Alberto0235/DRSSTC-Fiber-Optic-Interrupter/Hardware/KiCad/Interrupter/Fiber_Outputs.kicad_sch

## KiCad design Hardware/KiCad/Interrupter/Fiber_Outputs.kicad_sch (2026-04-12)

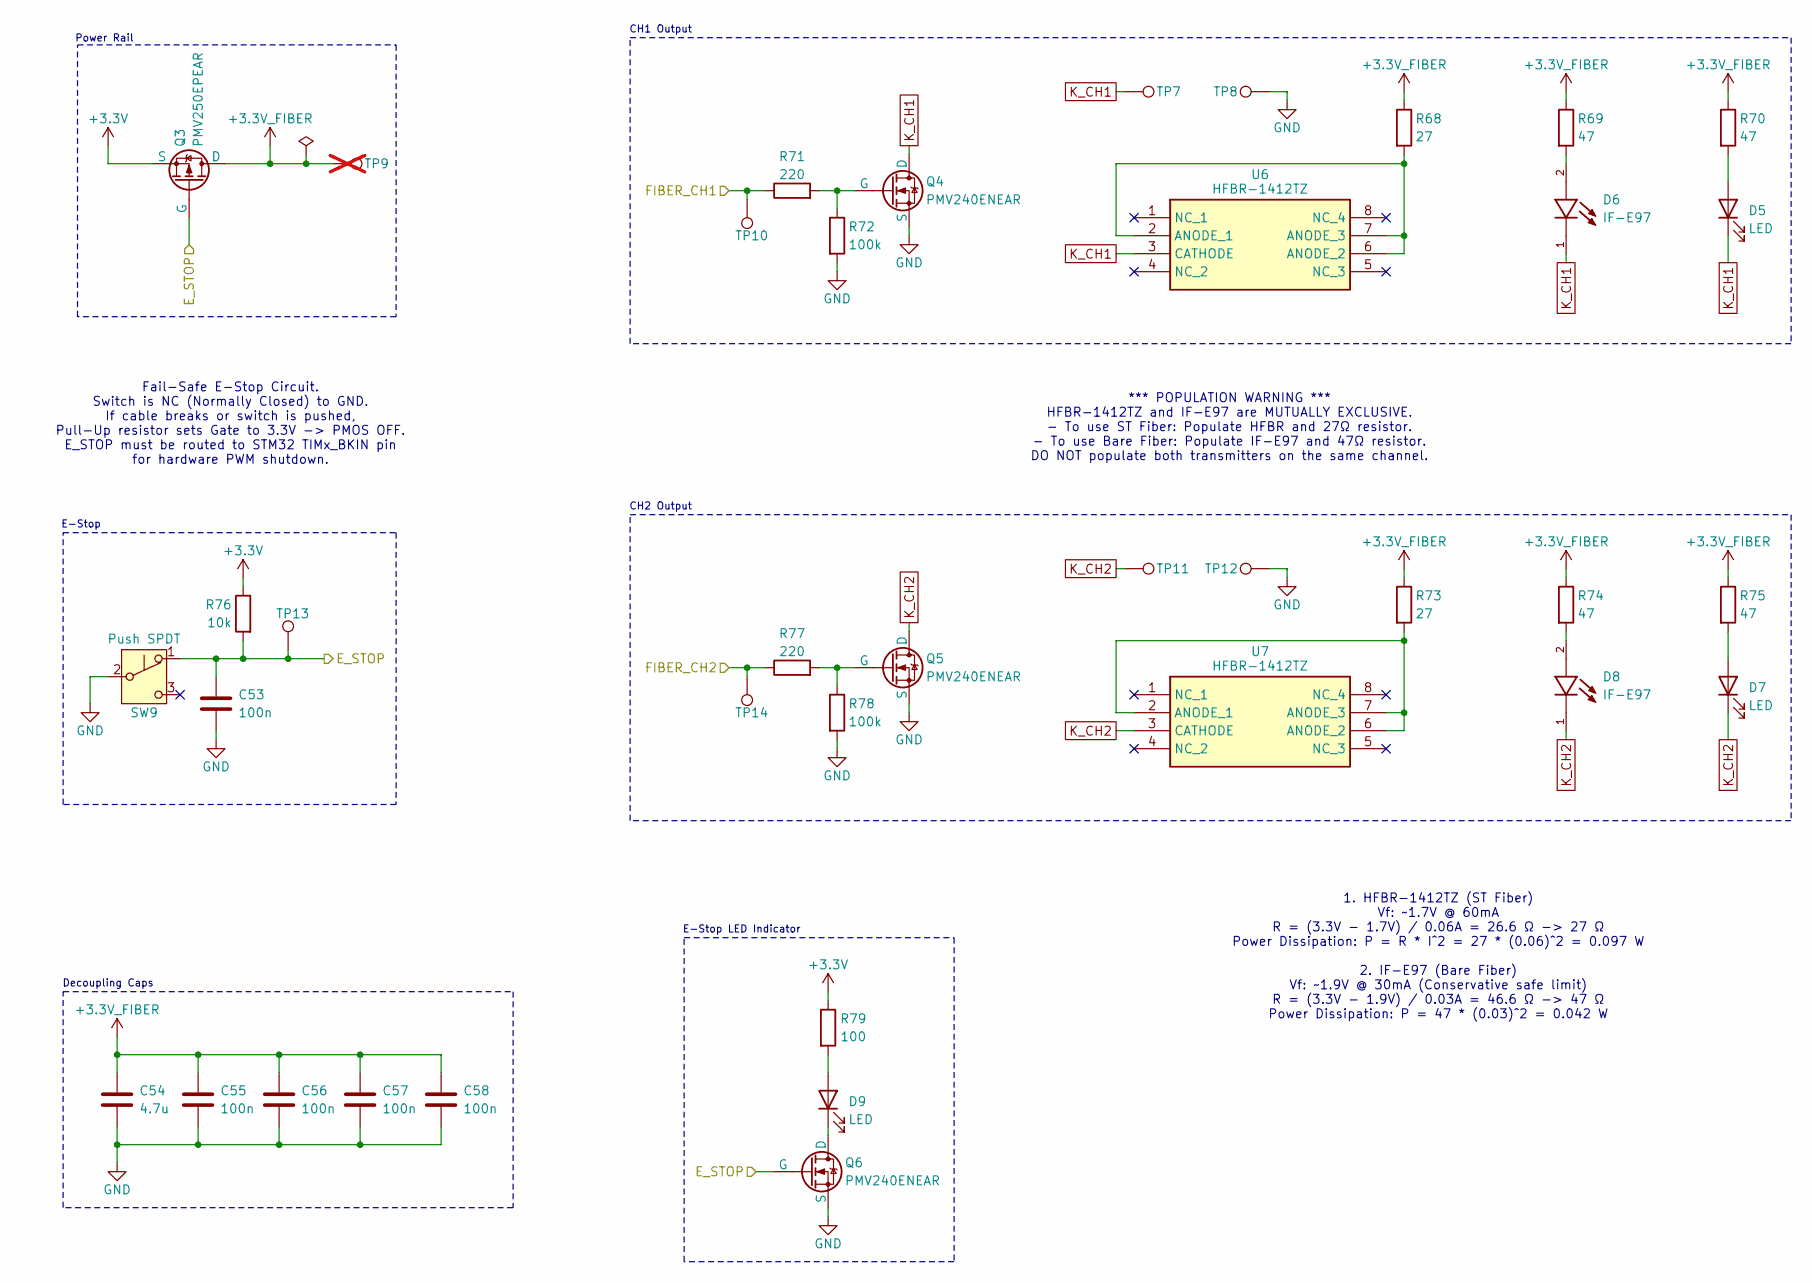
[picture p9: schematic Fiber_Outputs.kicad_sch]

Parts:
C53, C55, C56, C57, C58: 100n; C_0402_1005Metric; Manufacturer_Part_Number GRT155R71H104KE01J
C54: 4.7u; C_0805_2012Metric; Manufacturer_Part_Number GRM21BZ7YA475KE15K
D5, D7: LED; TOPLED E1608; Manufacturer_Part_Number KB DELSS2.12-THUH-34-2686
D6, D8: IF-E97; PARTREV 11/20
D9: LED; TOPLED E1608; Manufacturer_Part_Number KS DELPS1.22-TIVH-68-H3Q4-20-S
Q3: PMV250EPEAR; SOT-23; Manufacturer_Part_Number PMV250EPEA
Q4, Q5, Q6: PMV240ENEAR; SOT-23; Manufacturer_Part_Number PMV240ENEAR
R68, R73: 27; R_0805_2012Metric; Manufacturer_Part_Number ERJ-P06F27R0V
R69, R70, R74, R75: 47; R_0805_2012Metric; Manufacturer_Part_Number ERJ-P06F47R0V
R71, R77: 220; R_0402_1005Metric; Manufacturer_Part_Number AC0402FR-7W220RL
R72, R78: 100k; R_0402_1005Metric; Manufacturer_Part_Number AC0402FR-7W100KL
R76: 10k; R_0402_1005Metric; Manufacturer_Part_Number AC0402FR-0710KL
R79: 100; R_0402_1005Metric; Manufacturer_Part_Number AC0402FR-13100RL
SW9: Push SPDT; 8161SHCQE2; Manufacturer_Part_Number 8161SHCQE2
TP7, TP8, TP10, TP11, TP12, TP13, TP14: TestPoint; S275146R; Manufacturer_Part_Number S2751-46R
TP9: TestPoint; S275146R; Manufacturer_Part_Number S2751-46R; not fitted
U6, U7: HFBR-1412TZ; HFBR1412TMZ; Mouser Part Number 630-HFBR-1412TZ

Connections:
+3.3V: Q3.2 (S), R76.1, R79.1
+3.3V_FIBER: C54.1, C55.1, C56.1, C57.1, C58.1, Q3.3 (D), R68.1, R69.1, R70.1, R73.1, R74.1, R75.1, TP9.1
E_STOP: C53.1, Q3.1 (G), Q6.1 (G), R76.2, SW9.1 (A), TP13.1
FIBER_CH1: R71.1, TP10.1
FIBER_CH2: R77.1, TP14.1
GND: C53.2, C54.2, C55.2, C56.2, C57.2, C58.2, Q4.2 (S), Q5.2 (S), Q6.2 (S), R72.2, R78.2, SW9.2 (B), TP8.1, TP12.1
K_CH1: D5.1 (K), D6.1, Q4.3 (D), TP7.1, U6.3 (CATHODE)
K_CH2: D7.1 (K), D8.1, Q5.3 (D), TP11.1, U7.3 (CATHODE)
unnamed: D5.2 (A), R70.2
unnamed: D6.2, R69.2
unnamed: D7.2 (A), R75.2
unnamed: D8.2, R74.2
unnamed: D9.1 (K), Q6.3 (D)
unnamed: D9.2 (A), R79.2
unnamed: Q4.1 (G), R71.2, R72.1
unnamed: Q5.1 (G), R77.2, R78.1
unnamed: R68.2, U6.2 (ANODE_1), U6.6 (ANODE_2), U6.7 (ANODE_3)
unnamed: R73.2, U7.2 (ANODE_1), U7.6 (ANODE_2), U7.7 (ANODE_3)

Notes on the sheet:
Power Rail
CH1 Output
*** POPULATION WARNING *** HFBR-1412TZ and IF-E97 are MUTUALLY EXCLUSIVE. - To use ST Fiber: Populate HFBR and 27Ω resistor. - To use Bare Fiber: Populate IF-E97 and 47Ω resistor. DO NOT populate both transmitters on the same channel.
E-Stop LED Indicator
1. HFBR-1412TZ (ST Fiber) Vf: ~1.7V @ 60mA R = (3.3V - 1.7V) / 0.06A = 26.6 Ω -> 27 Ω Power Dissipation: P = R * I^2 = 27 * (0.06)^2 = 0.097 W 2. IF-E97 (Bare Fiber) Vf: ~1.9V @ 30mA (Conservative safe limit) R = (3.3V - 1.9V) / 0.03A = 46.6 Ω -> 47 Ω Power Dissipation: P = 47 * (0.03)^2 = 0.042 W
Fail-Safe E-Stop Circuit. Switch is NC (Normally Closed) to GND. If cable breaks or switch is pushed, Pull-Up resistor sets Gate to 3.3V -> PMOS OFF. E_STOP must be routed to STM32 TIMx_BKIN pin for hardware PWM shutdown.
CH2 Output
E-Stop
Decoupling Caps
