Alberto0235/DRSSTC-Fiber-Optic-Interrupter/Hardware/KiCad/Interrupter/Interrupter v1.2.kicad_sch

## KiCad design Hardware/KiCad/Interrupter/Interrupter v1.2.kicad_sch (2026-04-03)

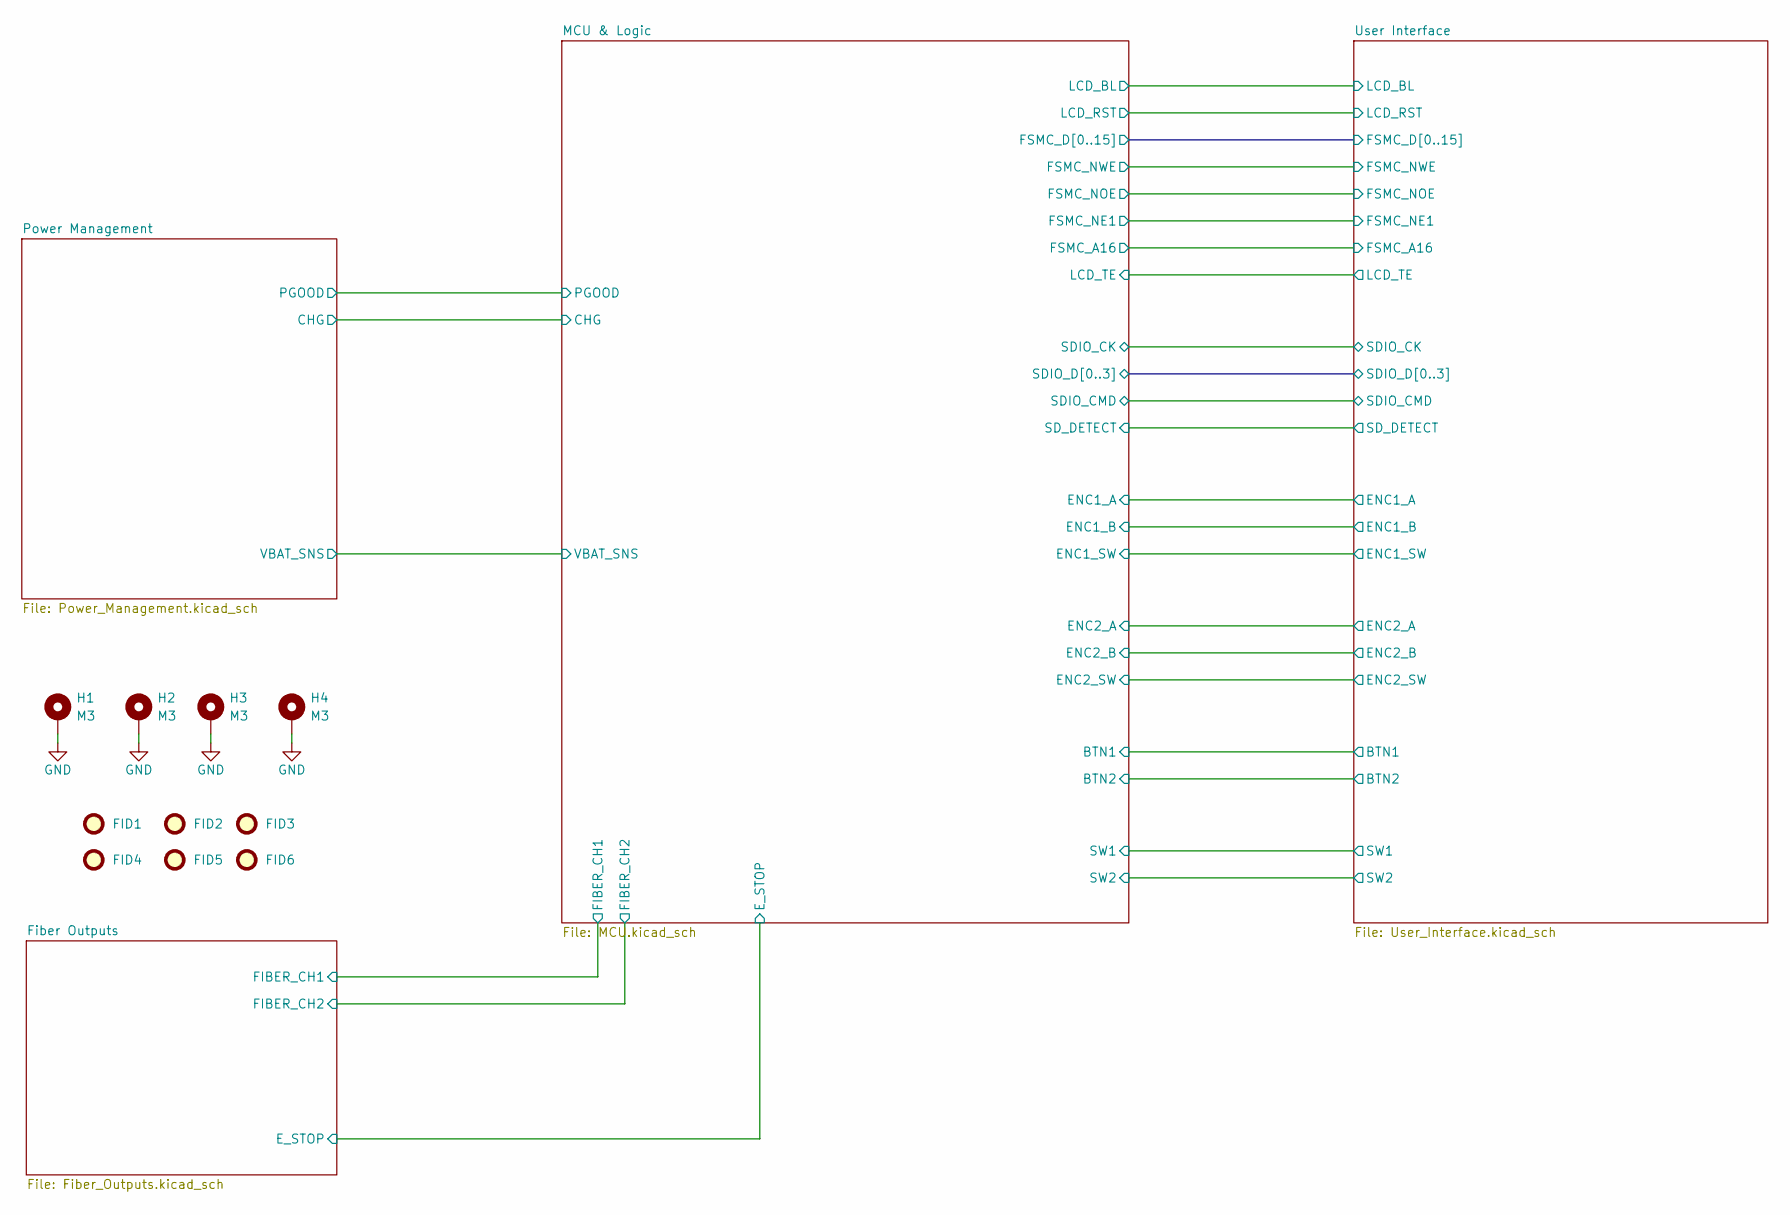
[picture p10: schematic Interrupter v1.2.kicad_sch]

Parts:
FID1, FID2, FID3, FID4, FID5, FID6: Fiducial; Fiducial_1mm_Mask2mm; Manufacturer_Part_Number Fiducial
H1, H2, H3, H4: M3; MountingHole_3.2mm_M3_Pad_Via; Manufacturer_Part_Number MountingHole-M3

Connections:
GND: H1.1, H2.1, H3.1, H4.1
