Alberto0235/DRSSTC-Fiber-Optic-Interrupter/Hardware/KiCad/Interrupter/mcu.kicad_sch

## KiCad design Hardware/KiCad/Interrupter/mcu.kicad_sch (2026-04-12)

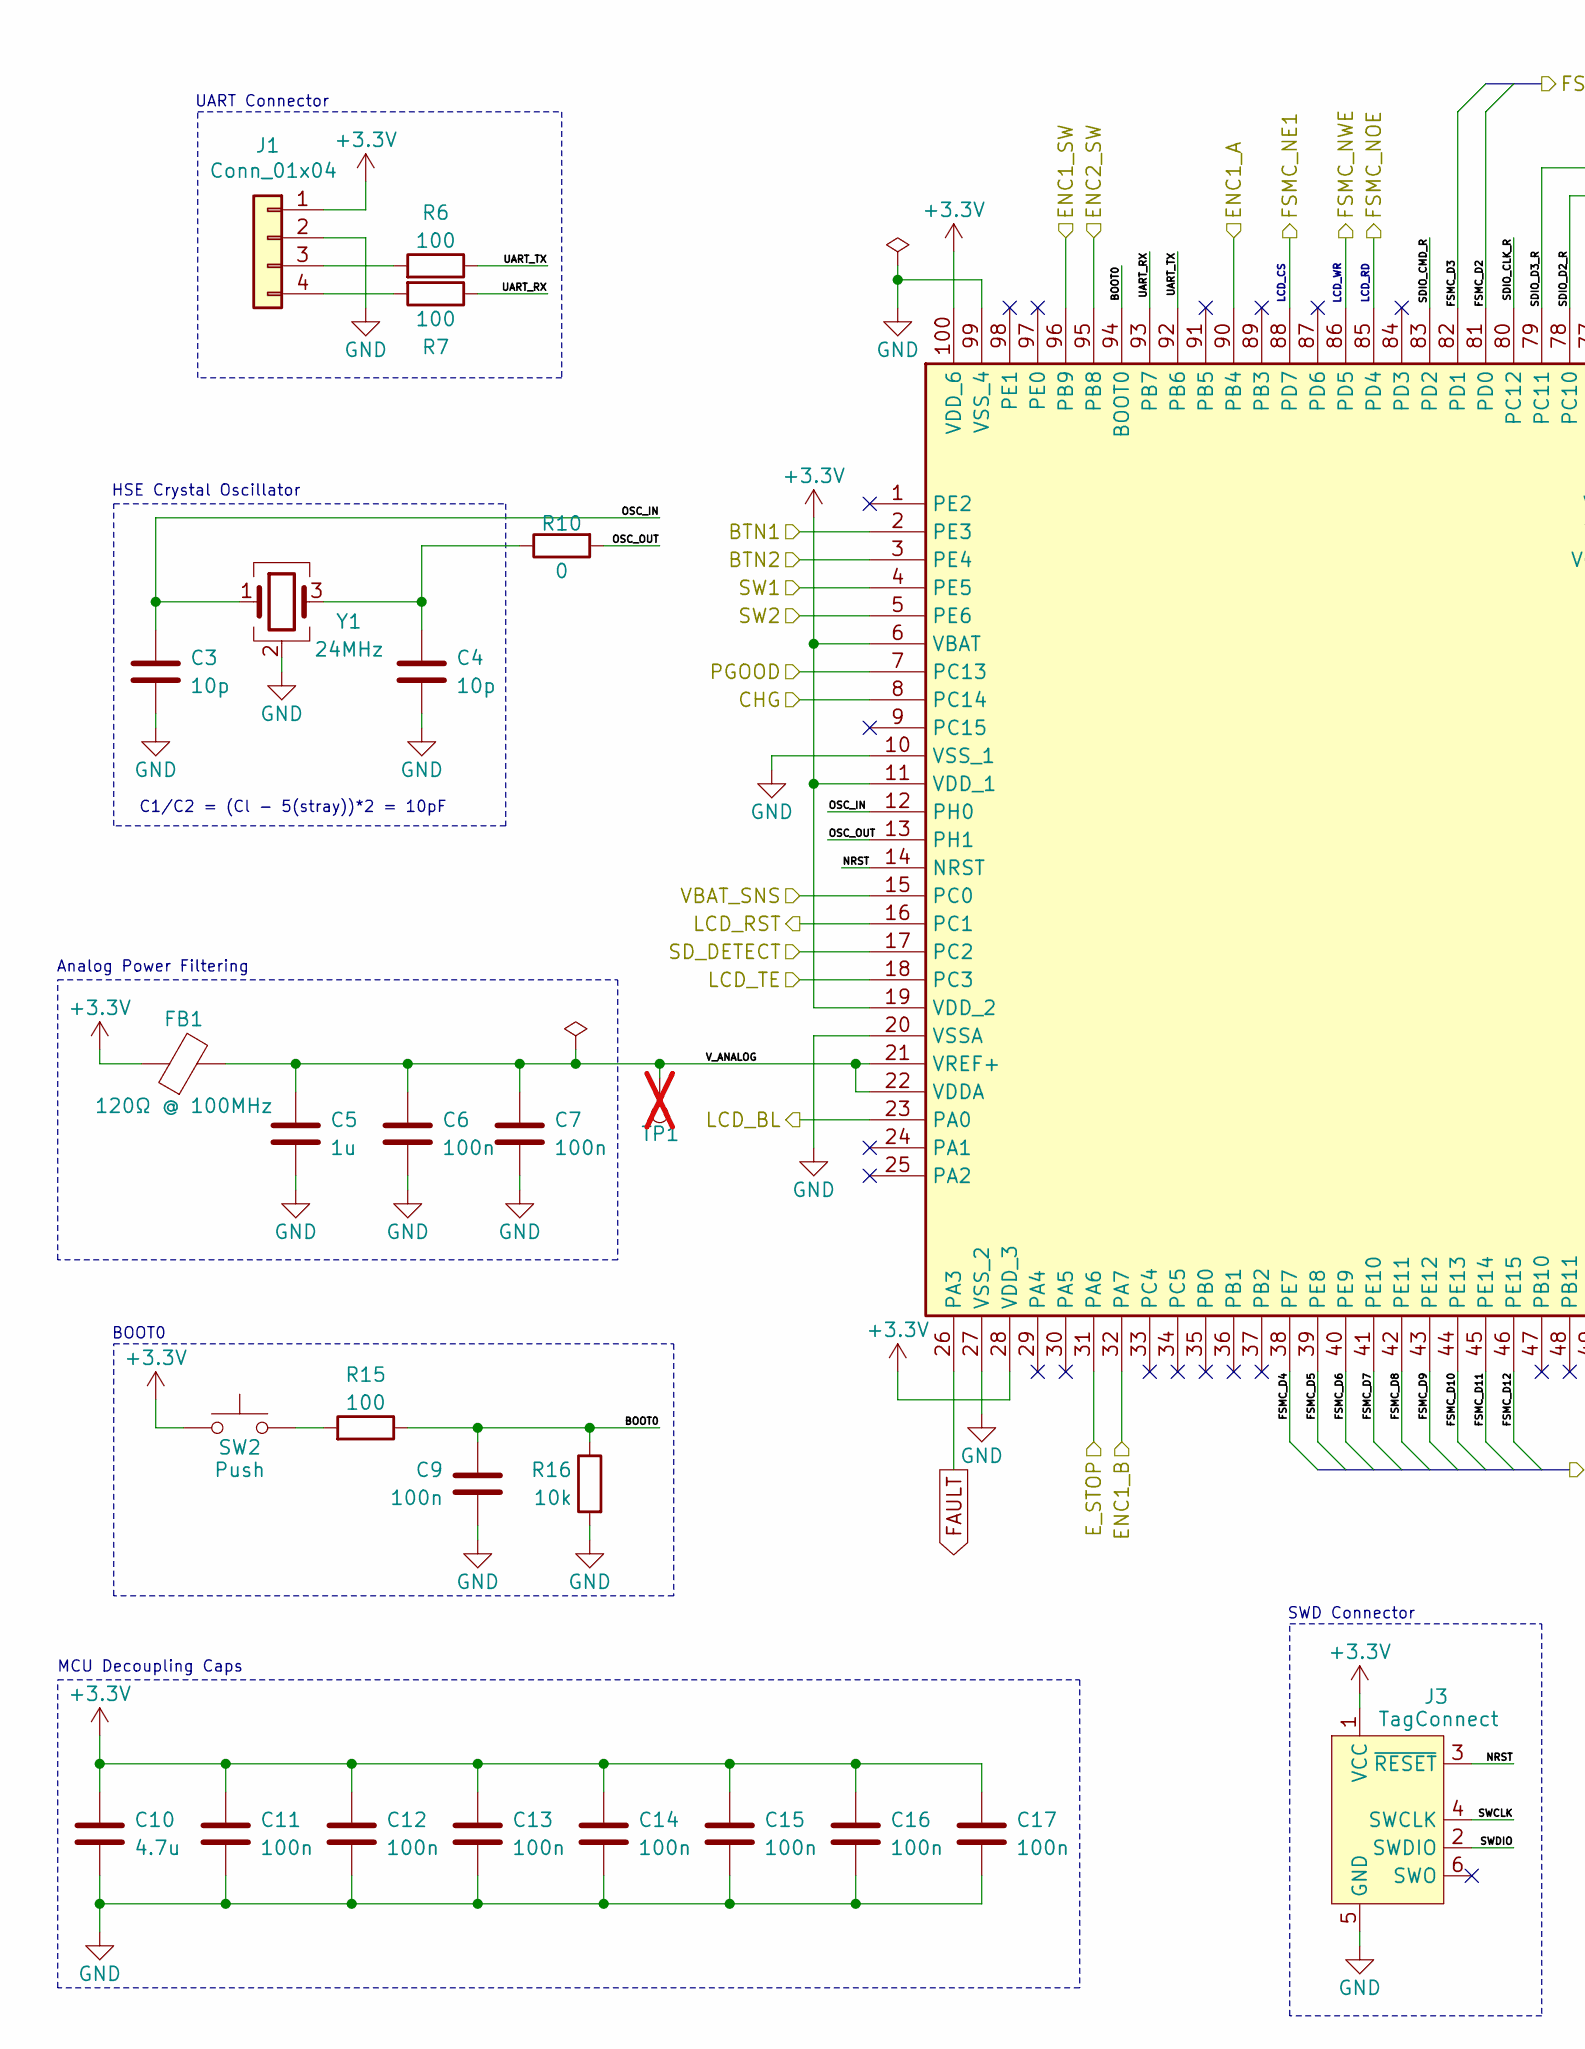
[picture p11: schematic mcu.kicad_sch, part in row 1, column 1]

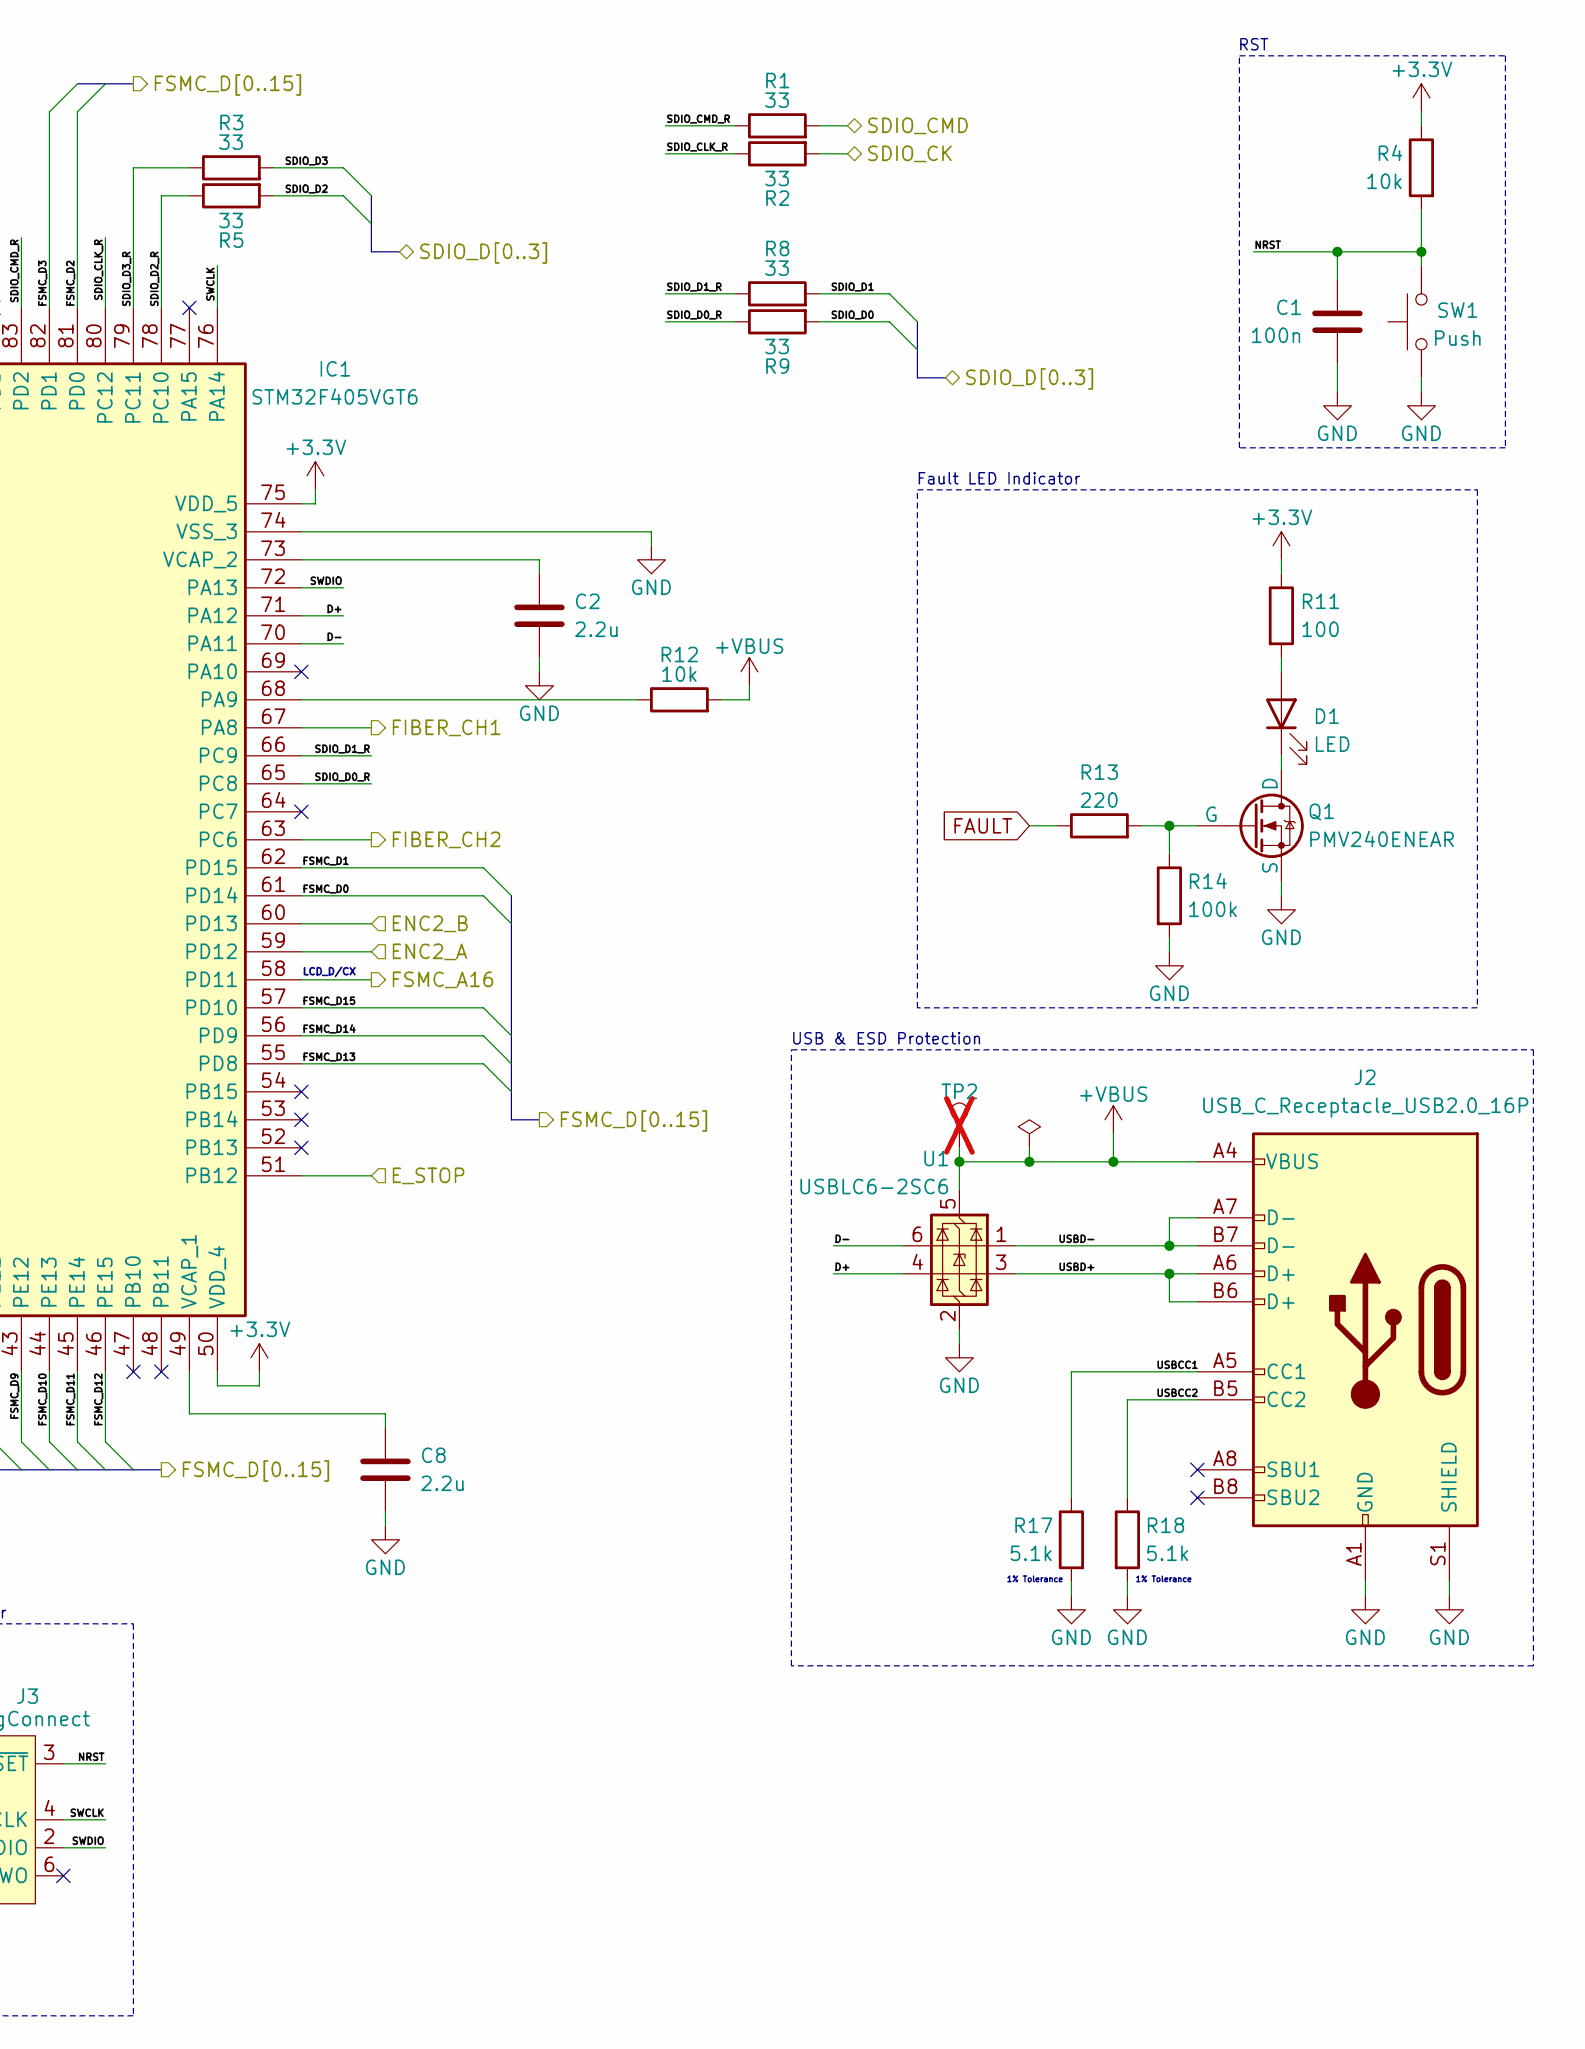
[picture p12: schematic mcu.kicad_sch, part in row 1, column 2]

Parts:
C1, C6, C7, C9, C11, C12, C13, C14, C15, C16, C17: 100n; C_0402_1005Metric; Manufacturer_Part_Number GRT155R71H104KE01J
C2, C8: 2.2u; C_0805_2012Metric; Manufacturer_Part_Number KGM21AR71E225KU
C3, C4: 10p; C_0402_1005Metric; Manufacturer_Part_Number GRM1555C1H100FA01D
C5: 1u; C_0603_1608Metric; Manufacturer_Part_Number C1608X7R1H105K080AB
C10: 4.7u; C_0805_2012Metric; Manufacturer_Part_Number GRM21BZ7YA475KE15K
D1: LED; TOPLED E1608; Manufacturer_Part_Number KS DELPS1.22-TIVH-68-H3Q4-20-S
FB1: 120Ω @ 100MHz; L_0603_1608Metric; Manufacturer_Part_Number BLM18SG121TZ1D
IC1: STM32F405VGT6; Mouser Part Number 511-STM32F405VGT6
J1: Conn_01x04; PinSocket_1x04_P2.00mm_Vertical
J2: USB_C_Receptacle_USB2.0_16P; USB_C_Receptacle_GCT_USB4105-xx-A_16P_TopMnt_Horizontal; Manufacturer_Part_Number USB4105-GF-A-120
J3: TagConnect; Tag-Connect_TC2030-IDC-NL_2x03_P1.27mm_Vertical
Q1: PMV240ENEAR; SOT-23; Manufacturer_Part_Number PMV240ENEAR
R1, R2, R3, R5, R8, R9: 33; R_0402_1005Metric; Manufacturer_Part_Number RCA040233R0FKEDSR
R4, R12, R16: 10k; R_0402_1005Metric; Manufacturer_Part_Number AC0402FR-0710KL
R6, R7, R11, R15: 100; R_0402_1005Metric; Manufacturer_Part_Number AC0402FR-13100RL
R10: 0; R_0402_1005Metric; Manufacturer_Part_Number CRCW04020000Z0ED
R13: 220; R_0402_1005Metric; Manufacturer_Part_Number AC0402FR-7W220RL
R14: 100k; R_0402_1005Metric; Manufacturer_Part_Number AC0402FR-7W100KL
R17, R18: 5.1k; R_0402_1005Metric; Manufacturer_Part_Number AF0402FR-075K1L
SW1, SW2: Push; PTS636SM43JSMTRLFS; Manufacturer_Part_Number PTS636SM43JSMTR LFS
TP1, TP2: TestPoint; S275146R; Manufacturer_Part_Number S2751-46R; not fitted
U1: USBLC6-2SC6; SOT-23-6; Manufacturer_Part_Number USBLC6-2SC6
Y1: 24MHz; Crystal_SMD_Abracon_ABM10-4Pin_2.5x2.0mm; Manufacturer_Part_Number ABM10N-24.0000MHZ-10-B1U-T3

Connections:
+3.3V: C10.1, C11.1, C12.1, C13.1, C14.1, C15.1, C16.1, C17.1, FB1.1, IC1.6 (VBAT), IC1.11 (VDD_1), IC1.19 (VDD_2), IC1.28 (VDD_3), IC1.50 (VDD_4), IC1.75 (VDD_5), IC1.100 (VDD_6), J1.1, J3.1 (VCC), R4.1, R11.1, SW2.1
+VBUS: J2.A4 (VBUS), J2.A9 (VBUS), J2.B4 (VBUS), J2.B9 (VBUS), R12.2, TP2.1, U1.5 (VBUS)
BOOT0: C9.1, IC1.94 (BOOT0), R15.1, R16.1
BTN1: IC1.2 (PE3)
BTN2: IC1.3 (PE4)
CHG: IC1.8 (PC14)
D+: IC1.71 (PA12), U1.4 (I/O2)
D-: IC1.70 (PA11), U1.6 (I/O1)
ENC1_A: IC1.90 (PB4)
ENC1_B: IC1.32 (PA7)
ENC1_SW: IC1.96 (PB9)
ENC2_A: IC1.59 (PD12)
ENC2_B: IC1.60 (PD13)
ENC2_SW: IC1.95 (PB8)
E_STOP: IC1.31 (PA6), IC1.51 (PB12)
FAULT: IC1.26 (PA3), R13.1
FIBER_CH1: IC1.67 (PA8)
FIBER_CH2: IC1.63 (PC6)
FSMC_A16: IC1.58 (PD11)
FSMC_D0: IC1.61 (PD14)
FSMC_D1: IC1.62 (PD15)
FSMC_D2: IC1.81 (PD0)
FSMC_D3: IC1.82 (PD1)
FSMC_D4: IC1.38 (PE7)
FSMC_D5: IC1.39 (PE8)
FSMC_D6: IC1.40 (PE9)
FSMC_D7: IC1.41 (PE10)
FSMC_D8: IC1.42 (PE11)
FSMC_D9: IC1.43 (PE12)
FSMC_D10: IC1.44 (PE13)
FSMC_D11: IC1.45 (PE14)
FSMC_D12: IC1.46 (PE15)
FSMC_D13: IC1.55 (PD8)
FSMC_D14: IC1.56 (PD9)
FSMC_D15: IC1.57 (PD10)
FSMC_NE1: IC1.88 (PD7)
FSMC_NOE: IC1.85 (PD4)
FSMC_NWE: IC1.86 (PD5)
GND: C1.2, C2.2, C3.2, C4.2, C5.2, C6.2, C7.2, C8.2, C9.2, C10.2, C11.2, C12.2, C13.2, C14.2, C15.2, C16.2, C17.2, IC1.10 (VSS_1), IC1.20 (VSSA), IC1.27 (VSS_2), IC1.74 (VSS_3), IC1.99 (VSS_4), J1.2, J2.A1 (GND), J2.A12 (GND), J2.B1 (GND), J2.B12 (GND), J2.S1 (SHIELD), J3.5 (GND), Q1.2 (S), R14.2, R16.2, R17.2, R18.2, SW1.1, U1.2 (GND), Y1.2 (G), Y1.4 (G)
LCD_BL: IC1.23 (PA0)
LCD_RST: IC1.16 (PC1)
LCD_TE: IC1.18 (PC3)
NRST: C1.1, IC1.14 (NRST), J3.3 (~RESET), R4.2, SW1.2
unnamed: C2.1, IC1.73 (VCAP_2)
unnamed: C4.1, R10.1, Y1.3
unnamed: C8.1, IC1.49 (VCAP_1)
unnamed: D1.1 (K), Q1.3 (D)
unnamed: D1.2 (A), R11.2
unnamed: IC1.68 (PA9), R12.1
unnamed: J1.3, R6.2
unnamed: J1.4, R7.2
unnamed: Q1.1 (G), R13.2, R14.1
unnamed: R15.2, SW2.2
OSC_IN: C3.1, IC1.12 (PH0), Y1.1
OSC_OUT: IC1.13 (PH1), R10.2
PGOOD: IC1.7 (PC13)
SDIO_CK: R2.2
SDIO_CLK_R: IC1.80 (PC12), R2.1
SDIO_CMD: R1.2
SDIO_CMD_R: IC1.83 (PD2), R1.1
SDIO_D0: R9.2
SDIO_D0_R: IC1.65 (PC8), R9.1
SDIO_D1: R8.2
SDIO_D1_R: IC1.66 (PC9), R8.1
SDIO_D2: R5.2
SDIO_D2_R: IC1.78 (PC10), R5.1
SDIO_D3: R3.2
SDIO_D3_R: IC1.79 (PC11), R3.1
SD_DETECT: IC1.17 (PC2)
SW1: IC1.4 (PE5)
SW2: IC1.5 (PE6)
SWCLK: IC1.76 (PA14), J3.4 (SWCLK)
SWDIO: IC1.72 (PA13), J3.2 (SWDIO)
UART_RX: IC1.93 (PB7), R7.1
UART_TX: IC1.92 (PB6), R6.1
USBCC1: J2.A5 (CC1), R17.1
USBCC2: J2.B5 (CC2), R18.1
USBD+: J2.A6 (D+), J2.B6 (D+), U1.3 (I/O2)
USBD-: J2.A7 (D-), J2.B7 (D-), U1.1 (I/O1)
VBAT_SNS: IC1.15 (PC0)
V_ANALOG: C5.1, C6.1, C7.1, FB1.2, IC1.21 (VREF+), IC1.22 (VDDA), TP1.1

Notes on the sheet:
BOOT0
1% Tolerance
Analog Power Filtering
USB & ESD Protection
C1/C2 = (Cl - 5(stray))*2 = 10pF
MCU Decoupling Caps
LCD_CS
Fault LED Indicator
LCD_D/CX
LCD_WR
SWD Connector
UART Connector
RST
HSE Crystal Oscillator
LCD_RD
