Alberto0235/DRSSTC-Fiber-Optic-Interrupter/Hardware/KiCad/Interrupter/power_management.kicad_sch

## KiCad design Hardware/KiCad/Interrupter/power_management.kicad_sch (2026-04-12)

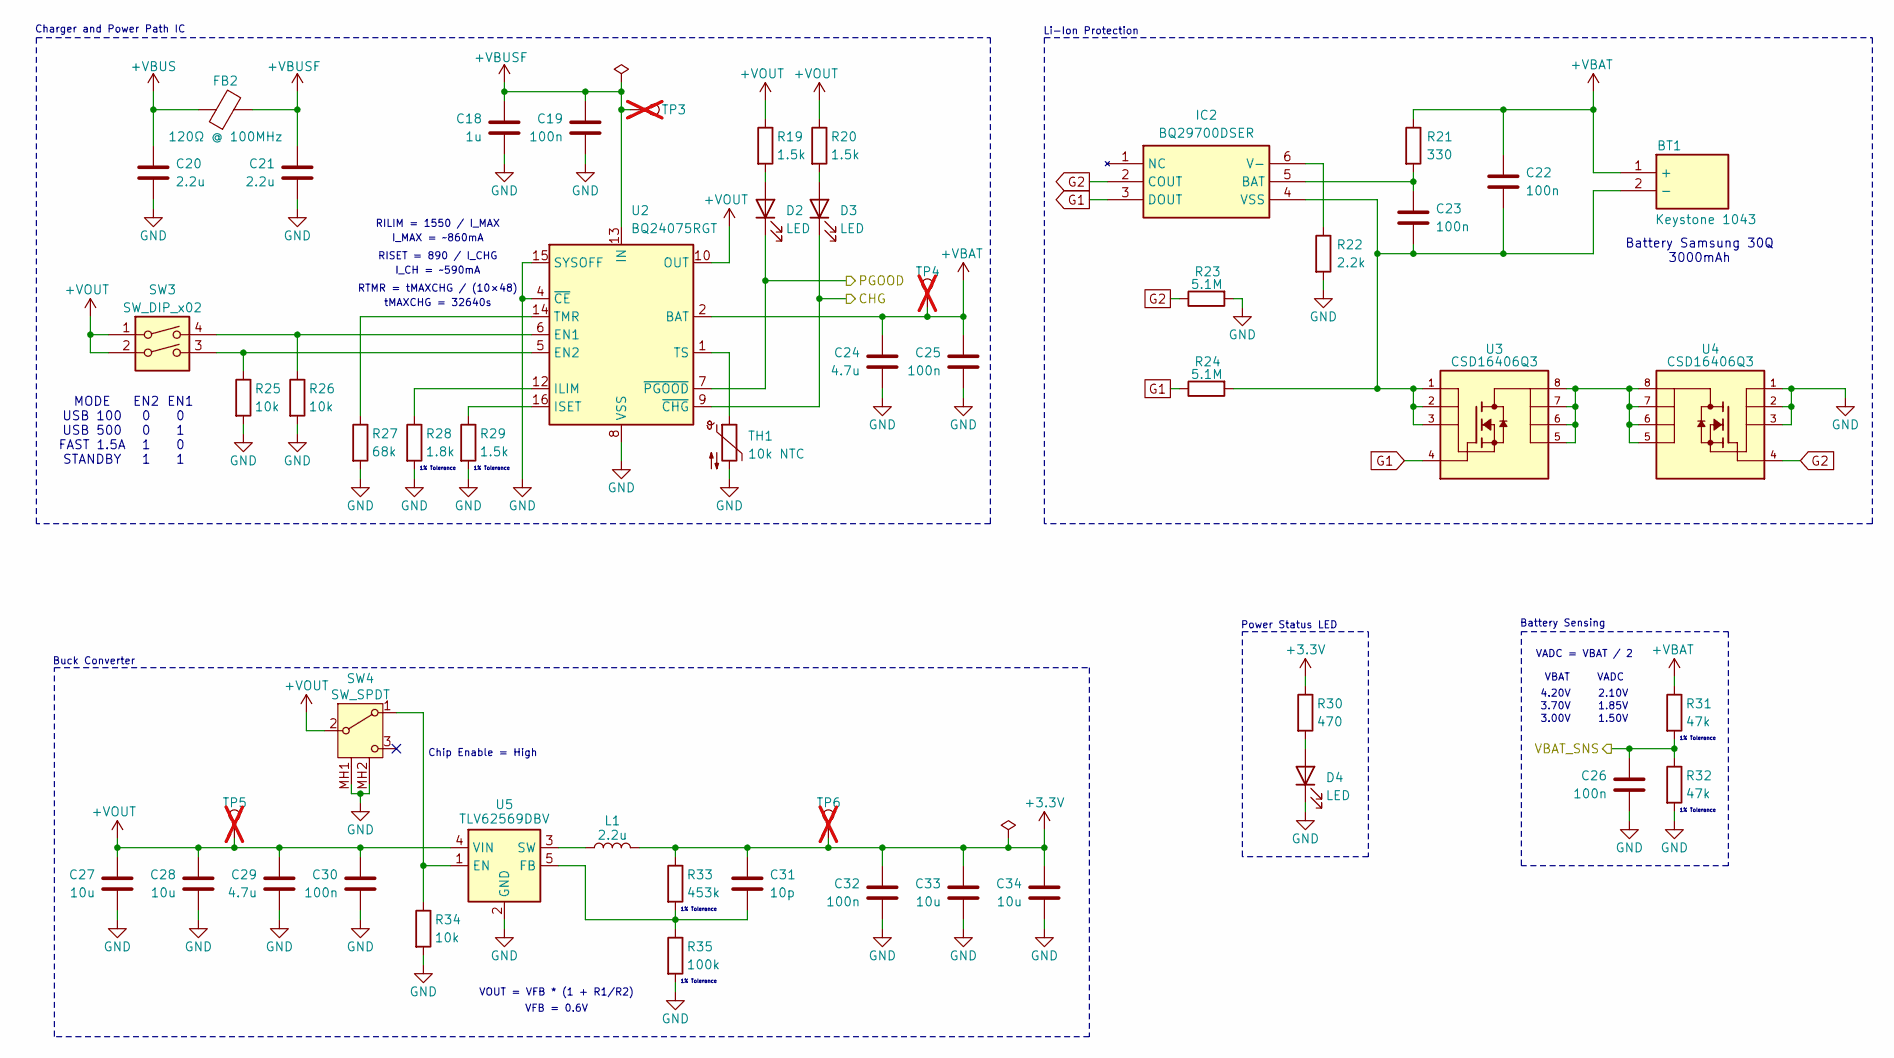
[picture p13: schematic power_management.kicad_sch]

Parts:
BT1: Keystone 1043; Mouser Part Number 534-1043
C18: 1u; C_0603_1608Metric; Manufacturer_Part_Number C1608X7R1H105K080AB
C19, C22, C23, C25, C26, C30, C32: 100n; C_0402_1005Metric; Manufacturer_Part_Number GRT155R71H104KE01J
C20, C21: 2.2u; C_0805_2012Metric; Manufacturer_Part_Number KGM21AR71E225KU
C24, C29: 4.7u; C_0805_2012Metric; Manufacturer_Part_Number GRM21BZ7YA475KE15K
C27, C28, C33, C34: 10u; C_0805_2012Metric; Manufacturer_Part_Number GRM21BZ71E106KE15L
C31: 10p; C_0402_1005Metric; Manufacturer_Part_Number GRM1555C1H100FA01D
D2, D4: LED; TOPLED E1608; Manufacturer_Part_Number KT DELSS1.12-AYBZ-36-N626
D3: LED; TOPLED E1608; Manufacturer_Part_Number KO DELPS1.22-UGVI-24-H3Q4-20-S
FB2: 120Ω @ 100MHz; L_0603_1608Metric; Manufacturer_Part_Number BLM18SG121TZ1D
IC2: BQ29700DSER; BQ29700; Mouser Part Number 595-BQ29700DSER
L1: 2.2u; ETQ-P3M2R2HFP; Manufacturer_Part_Number ETQ-P3M2R2HFP
R19, R20, R29: 1.5k; R_0402_1005Metric; Manufacturer_Part_Number AC0402FR-7W1K5L
R21: 330; R_0402_1005Metric; Manufacturer_Part_Number AC0402FR-7W330RL
R22: 2.2k; R_0402_1005Metric; Manufacturer_Part_Number AF0402FR-072K2L
R23, R24: 5.1M; R_0402_1005Metric; Manufacturer_Part_Number AF0402FR-075M1L
R25, R26, R34: 10k; R_0402_1005Metric; Manufacturer_Part_Number AC0402FR-0710KL
R27: 68k; R_0402_1005Metric; Manufacturer_Part_Number AC0402FR-7W68KL
R28: 1.8k; R_0402_1005Metric; Manufacturer_Part_Number AC0402FR-071K8L
R30: 470; R_0402_1005Metric; Manufacturer_Part_Number AC0402FR-7W470RL
R31, R32: 47k; R_0402_1005Metric; Manufacturer_Part_Number CRCW040247K0FKED
R33: 453k; R_0402_1005Metric; Manufacturer_Part_Number ERJ-2RKF4533X
R35: 100k; R_0402_1005Metric; Manufacturer_Part_Number AC0402FR-7W100KL
SW3: SW_DIP_x02; A6S-2104-H; Manufacturer_Part_Number A6S-2104-H
SW4: SW_SPDT; EG1206; Manufacturer_Part_Number EG1206
TH1: 10k NTC; R_0603_1608Metric; Manufacturer_Part_Number NTCG163JF103FT1A
TP3, TP4, TP5, TP6: TestPoint; S275146R; Manufacturer_Part_Number S2751-46R; not fitted
U2: BQ24075RGT; VQFN-16-1EP_3x3mm_P0.5mm_EP1.6x1.6mm; Manufacturer_Part_Number BQ24075RGTR
U3, U4: CSD16406Q3; Manufacturer_Part_Number CSD16406Q3
U5: TLV62569DBV; SOT-23-5; Manufacturer_Part_Number TLV62569DBVR

Connections:
+3.3V: C31.1, C32.1, C33.1, C34.1, L1.2, R30.1, R33.1, TP6.1
+VBAT: BT1.1 (+), C22.1, C24.1, C25.1, R21.1, R31.1, TP4.1, U2.2 (BAT), U2.3 (BAT)
+VBUS: C20.1, FB2.1
+VBUSF: C18.1, C19.1, C21.1, FB2.2, TP3.1, U2.13 (IN)
+VOUT: C27.1, C28.1, C29.1, C30.1, R19.1, R20.1, SW3.1, SW3.2, SW4.2 (B), TP5.1, U2.10 (OUT), U2.11 (OUT), U5.4 (VIN)
CHG: D3.1 (K), U2.9 (~CHG)
G1: IC2.3 (DOUT), R24.1, U3.4
G2: IC2.2 (COUT), R23.1, U4.4
GND: C18.2, C19.2, C20.2, C21.2, C24.2, C25.2, C26.2, C27.2, C28.2, C29.2, C30.2, C32.2, C33.2, C34.2, D4.1 (K), R22.2, R23.2, R25.2, R26.2, R27.2, R28.2, R29.2, R32.2, R34.2, R35.2, SW4.MH1 (D), SW4.MH2 (E), TH1.2, U2.4 (~CE), U2.8 (VSS), U2.15 (SYSOFF), U2.17 (VSS), U4.1, U4.2, U4.3, U5.2 (GND)
unnamed: BT1.2 (-), C22.2, C23.2, IC2.4 (VSS), R24.2, U3.1, U3.2, U3.3
unnamed: C23.1, IC2.5 (BAT), R21.2
unnamed: C31.2, R33.2, R35.1, U5.5 (FB)
unnamed: D2.2 (A), R19.2
unnamed: D3.2 (A), R20.2
unnamed: D4.2 (A), R30.2
unnamed: IC2.6 (V-), R22.1
unnamed: L1.1, U5.3 (SW)
unnamed: R25.1, SW3.3, U2.5 (EN2)
unnamed: R26.1, SW3.4, U2.6 (EN1)
unnamed: R27.1, U2.14 (TMR)
unnamed: R28.1, U2.12 (ILIM)
unnamed: R29.1, U2.16 (ISET)
unnamed: R34.1, SW4.1 (A), U5.1 (EN)
unnamed: TH1.1, U2.1 (TS)
unnamed: U3.5, U3.6, U3.7, U3.8, U4.5, U4.6, U4.7, U4.8
PGOOD: D2.1 (K), U2.7 (~PGOOD)
VBAT_SNS: C26.1, R31.2, R32.1

Notes on the sheet:
MODE USB 100 USB 500 FAST 1.5A STANDBY
1% Tolerance
Battery Samsung 30Q 3000mAh
EN2 0 0 1 1
Buck Converter
EN1 0 1 0 1
Chip Enable = High
Battery Sensing
I_CH = ~590mA
3.70V 1.85V
4.20V 2.10V
tMAXCHG = 32640s
RTMR  = tMAXCHG  / (10×48)
Li-Ion Protection
Power Status LED
Charger and Power Path IC
VOUT = VFB * (1 + R1/R2)
VFB = 0.6V
I_MAX = ~860mA
RISET = 890 / I_CHG
VADC = VBAT / 2
3.00V 1.50V
VBAT VADC
RILIM = 1550 / I_MAX
