Alberto0235/DRSSTC-Fiber-Optic-Interrupter/Hardware/KiCad/Interrupter/user_interface.kicad_sch

## KiCad design Hardware/KiCad/Interrupter/user_interface.kicad_sch (2026-04-12)

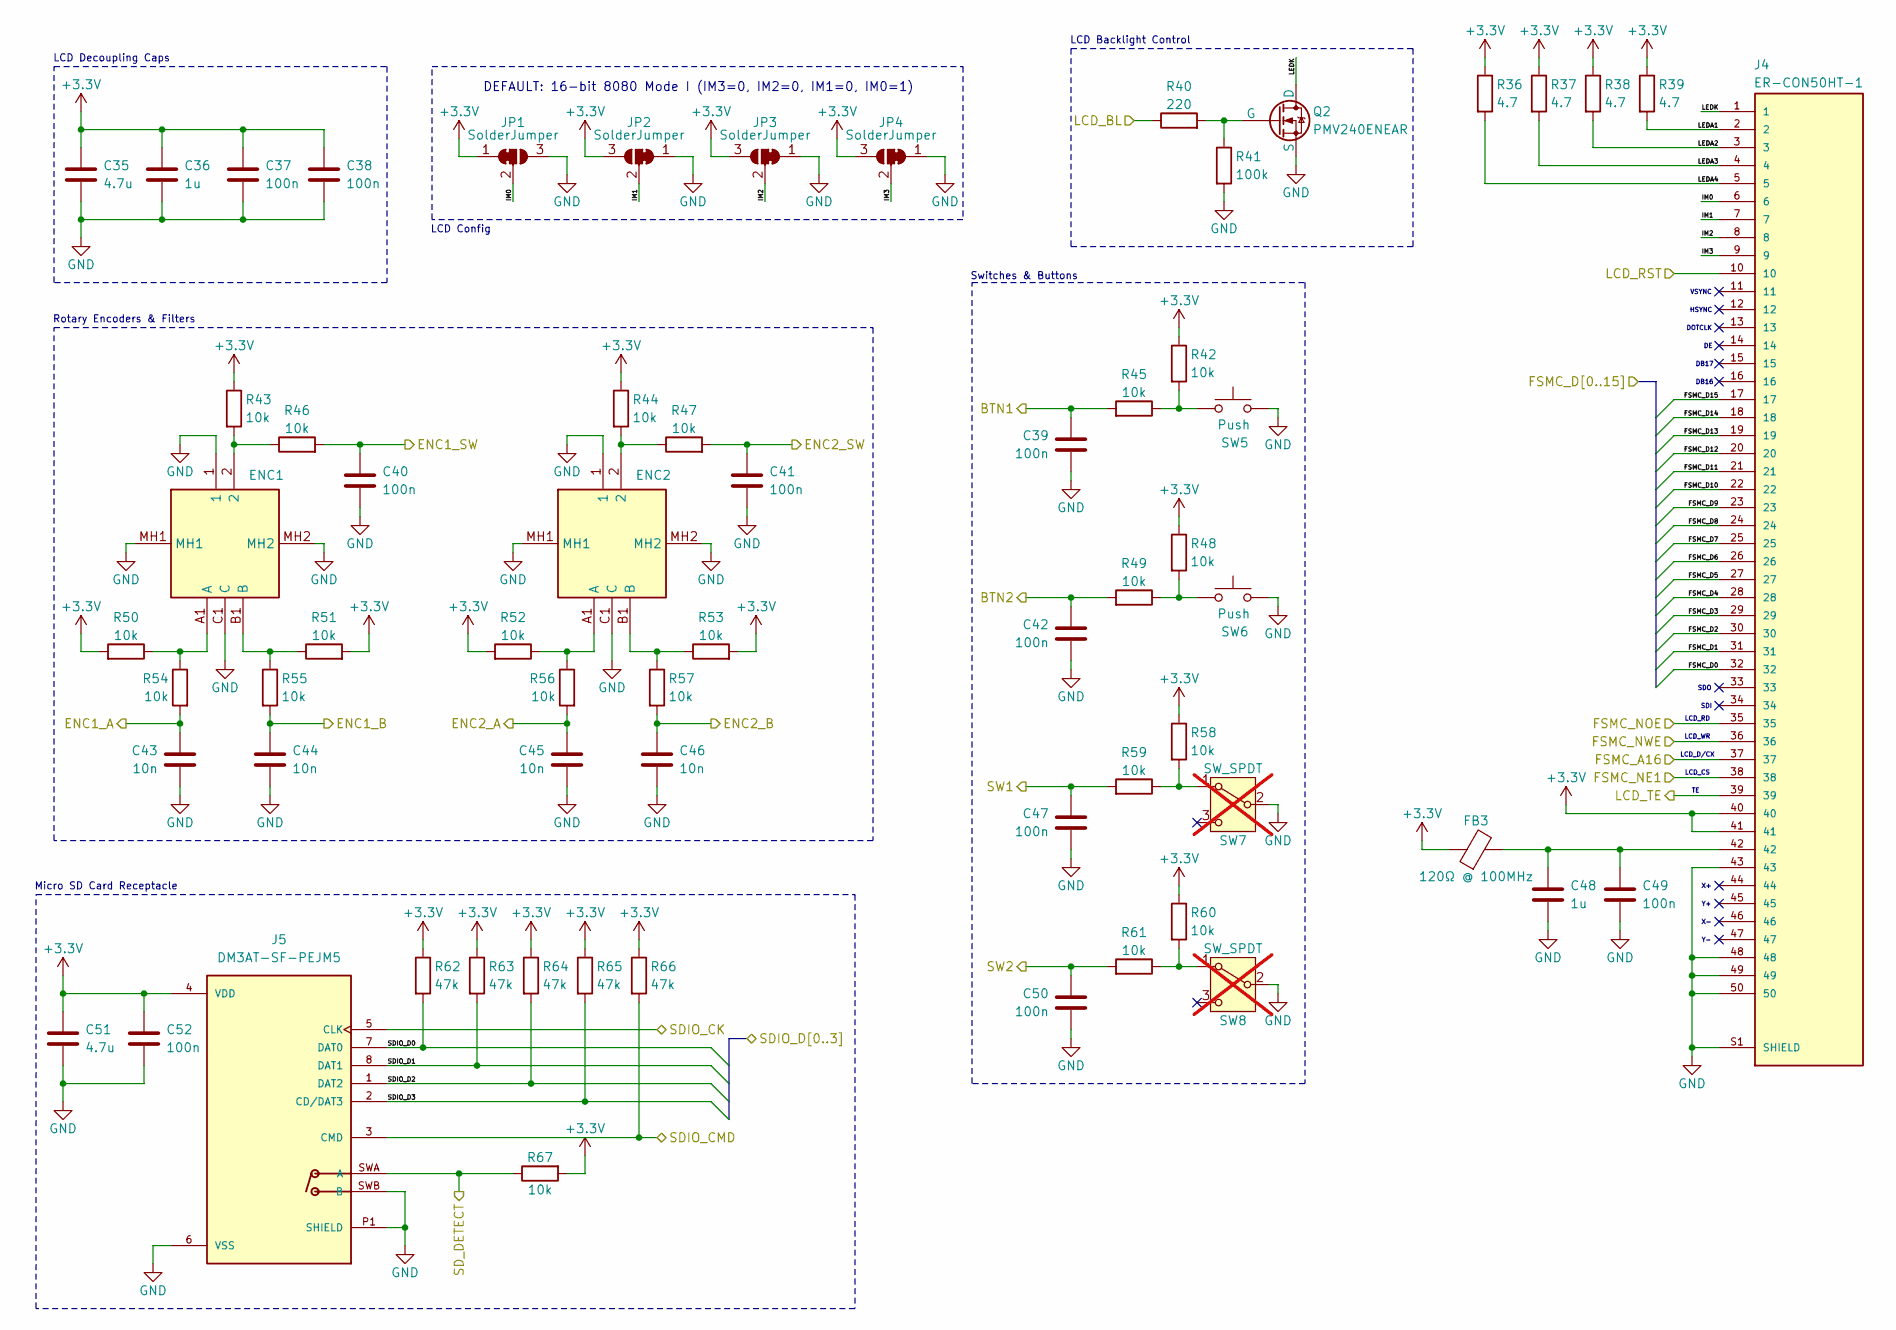
[picture p14: schematic user_interface.kicad_sch]

Parts:
C35, C51: 4.7u; C_0805_2012Metric; Manufacturer_Part_Number GRM21BZ7YA475KE15K
C36, C48: 1u; C_0603_1608Metric; Manufacturer_Part_Number C1608X7R1H105K080AB
C37, C38, C39, C40, C41, C42, C47, C49, C50, C52: 100n; C_0402_1005Metric; Manufacturer_Part_Number GRT155R71H104KE01J
C43, C44, C45, C46: 10n; C_0603_1608Metric; Manufacturer_Part_Number KAF15AR71H103JM
ENC1, ENC2: PEC11R-4220F-S0024; PEC11R4220FS0024; Mouser Part Number 652-PEC11R-4220F-S24
FB3: 120Ω @ 100MHz; L_0603_1608Metric; Manufacturer_Part_Number BLM18SG121TZ1D
J4: ER-CON50HT-1; PARTREV 1.0
J5: DM3AT-SF-PEJM5; PARTREV 20200913
JP1, JP2, JP3, JP4: SolderJumper; SolderJumper-3_P1.3mm_Bridged2Bar12_RoundedPad1.0x1.5mm_Num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; Manufacturer_Part_Number SolderJumper
Q2: PMV240ENEAR; SOT-23; Manufacturer_Part_Number PMV240ENEAR
R36, R37, R38, R39: 4.7; R_0402_1005Metric; Manufacturer_Part_Number SR0402FR-7T4R7L
R40: 220; R_0402_1005Metric; Manufacturer_Part_Number AC0402FR-7W220RL
R41: 100k; R_0402_1005Metric; Manufacturer_Part_Number AC0402FR-7W100KL
R42, R43, R44, R45, R46, R47, R48, R49, R50, R51, R52, R53, R54, R55, R56, R57, R58, R59, R60, R61, R67: 10k; R_0402_1005Metric; Manufacturer_Part_Number AC0402FR-0710KL
R62, R63, R64, R65, R66: 47k; R_0402_1005Metric; Manufacturer_Part_Number CRCW040247K0FKED
SW5, SW6: Push; B3F_4050; Manufacturer_Part_Number B3F-4050
SW7, SW8: SW_SPDT; 100SP1T1B1M2REH; Manufacturer_Part_Number 100SP1T1B1M2REH; not fitted

Connections:
+3.3V: C35.1, C36.1, C37.1, C38.1, C51.1, C52.1, FB3.1, J4.40, J4.41, J5.4 (VDD), JP1.1 (A), JP2.3 (B), JP3.3 (B), JP4.3 (B), R36.1, R37.1, R38.1, R39.1, R42.1, R43.1, R44.1, R48.1, R50.2, R51.2, R52.2, R53.2, R58.1, R60.1, R62.1, R63.1, R64.1, R65.1, R66.1, R67.2
BTN1: C39.1, R45.2
BTN2: C42.1, R49.2
ENC1_A: C43.1, R54.2
ENC1_B: C44.1, R55.2
ENC1_SW: C40.1, R46.2
ENC2_A: C45.1, R56.2
ENC2_B: C46.1, R57.2
ENC2_SW: C41.1, R47.2
FSMC_A16: J4.37
FSMC_D0: J4.32
FSMC_D1: J4.31
FSMC_D2: J4.30
FSMC_D3: J4.29
FSMC_D4: J4.28
FSMC_D5: J4.27
FSMC_D6: J4.26
FSMC_D7: J4.25
FSMC_D8: J4.24
FSMC_D9: J4.23
FSMC_D10: J4.22
FSMC_D11: J4.21
FSMC_D12: J4.20
FSMC_D13: J4.19
FSMC_D14: J4.18
FSMC_D15: J4.17
FSMC_NE1: J4.38
FSMC_NOE: J4.35
FSMC_NWE: J4.36
GND: C35.2, C36.2, C37.2, C38.2, C39.2, C40.2, C41.2, C42.2, C43.2, C44.2, C45.2, C46.2, C47.2, C48.2, C49.2, C50.2, C51.2, C52.2, ENC1.1, ENC1.C1 (C), ENC1.MH1, ENC1.MH2, ENC2.1, ENC2.C1 (C), ENC2.MH1, ENC2.MH2, J4.43, J4.48, J4.49, J4.50, J4.S1 (SHIELD), J4.S2 (SHIELD), J5.6 (VSS), J5.P1 (SHIELD), J5.P2 (SHIELD), J5.P3 (SHIELD), J5.P4 (SHIELD), J5.SWB (B), JP1.3 (B), JP2.1 (A), JP3.1 (A), JP4.1 (A), Q2.2 (S), R41.2, SW5.1, SW5.2, SW6.1, SW6.2, SW7.2 (B), SW8.2 (B)
IM0: J4.6, JP1.2 (C)
IM1: J4.7, JP2.2 (C)
IM2: J4.8, JP3.2 (C)
IM3: J4.9, JP4.2 (C)
LCD_BL: R40.1
LCD_RST: J4.10
LCD_TE: J4.39
LEDA1: J4.2, R39.2
LEDA2: J4.3, R38.2
LEDA3: J4.4, R37.2
LEDA4: J4.5, R36.2
LEDK: J4.1, Q2.3 (D)
unnamed: C48.1, C49.1, FB3.2, J4.42
unnamed: ENC1.2, R43.2, R46.1
unnamed: ENC1.A1 (A), R50.1, R54.1
unnamed: ENC1.B1 (B), R51.1, R55.1
unnamed: ENC2.2, R44.2, R47.1
unnamed: ENC2.A1 (A), R52.1, R56.1
unnamed: ENC2.B1 (B), R53.1, R57.1
unnamed: Q2.1 (G), R40.2, R41.1
unnamed: R42.2, R45.1, SW5.3, SW5.4
unnamed: R48.2, R49.1, SW6.3, SW6.4
unnamed: R58.2, R59.1, SW7.1 (A)
unnamed: R60.2, R61.1, SW8.1 (A)
SDIO_CK: J5.5 (CLK)
SDIO_CMD: J5.3 (CMD), R66.2
SDIO_D0: J5.7 (DAT0), R62.2
SDIO_D1: J5.8 (DAT1), R63.2
SDIO_D2: J5.1 (DAT2), R64.2
SDIO_D3: J5.2 (CD/DAT3), R65.2
SD_DETECT: J5.SWA (A), R67.1
SW1: C47.1, R59.2
SW2: C50.1, R61.2

Notes on the sheet:
VSYNC
LCD_WR
LCD_CS
LCD Decoupling Caps
LCD_D/CX
DOTCLK
Switches & Buttons
SDI
Micro SD Card Receptacle
HSYNC
DB17
DB16
DEFAULT: 16-bit 8080 Mode I (IM3=0, IM2=0, IM1=0, IM0=1)
SDO
LCD Config
Rotary Encoders & Filters
LCD_RD
LCD Backlight Control
